CMBSTEAMlab/sm_project/Enclosures/protoboard_test.stl

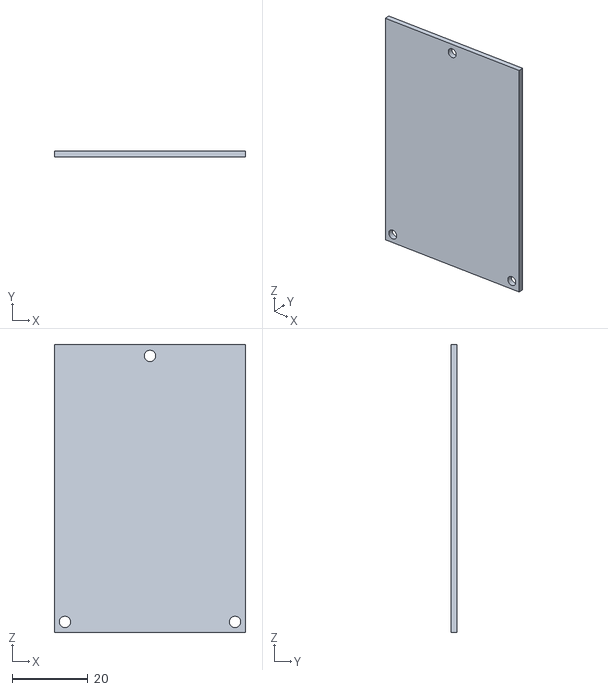
[picture p19: CAD file, 2018-03-08]
Enclosures/protoboard_test.stl
50.5 x 1.70 x 76.0
