CMBSTEAMlab/sm_project/Enclosures/all.stl

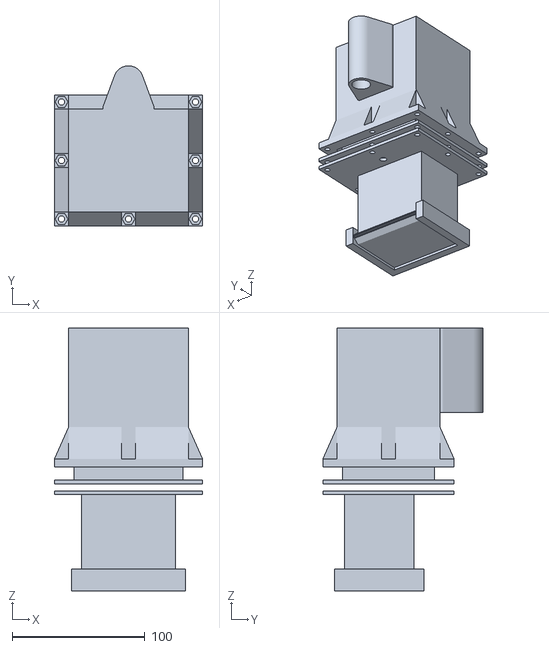
[picture p20: CAD file, 2018-03-08]
Enclosures/all.stl
111.6 x 120.7 x 198.1
