CMBSTEAMlab/sm_project/Enclosures/bottom_guard.stl

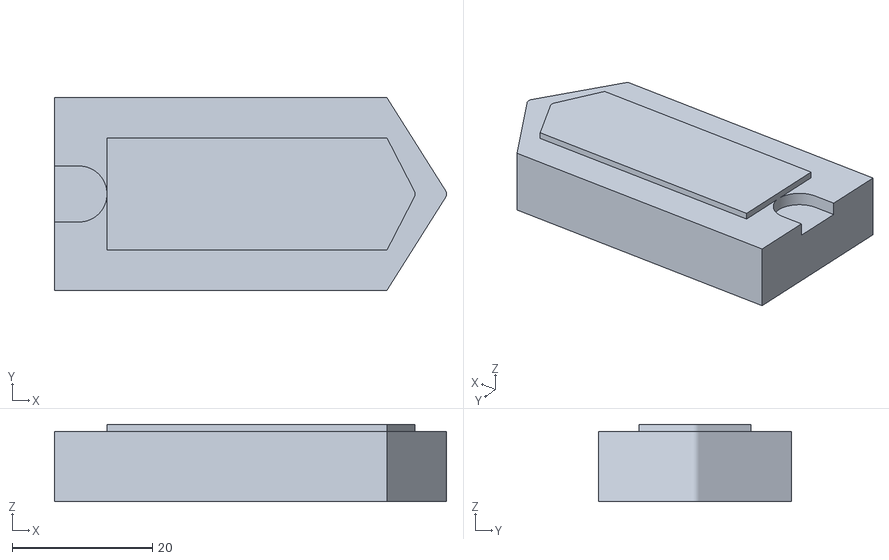
[picture p21: CAD file, 2018-03-08]
Enclosures/bottom_guard.stl
56.0 x 27.5 x 11.0
