CMBSTEAMlab/sm_project/Enclosures/lid_test1.stl

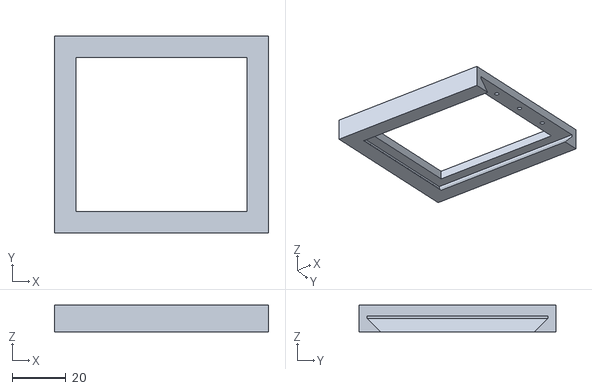
[picture p22: CAD file, 2018-03-08]
Enclosures/lid_test1.stl
79.5 x 73.2 x 10.0
