CMBSTEAMlab/sm_project/Enclosures/enclosure_battery_base.stl

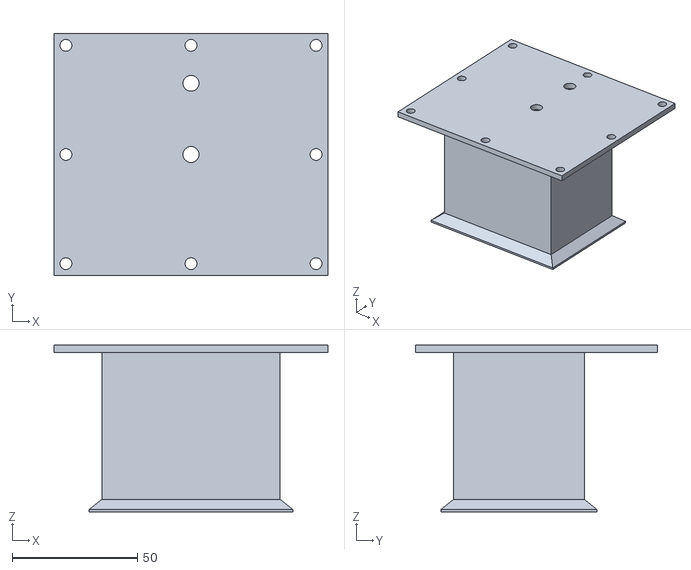
[picture p23: CAD file, 2018-03-08]
Enclosures/enclosure_battery_base.stl
109.2 x 96.5 x 66.5
